Tianming-Liu/CASA0016_ScreenTimer/Src/flip_timer.jpg

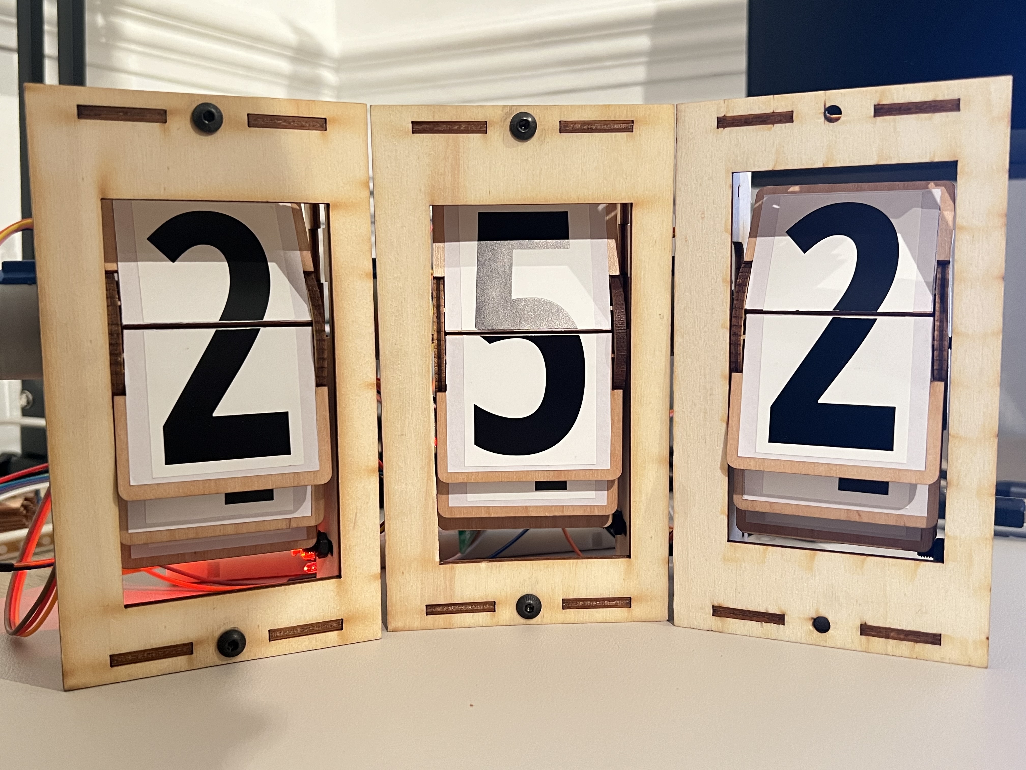
Src/flip_timer.jpg
