Tianming-Liu/CASA0016_ScreenTimer/Src/top00.jpg

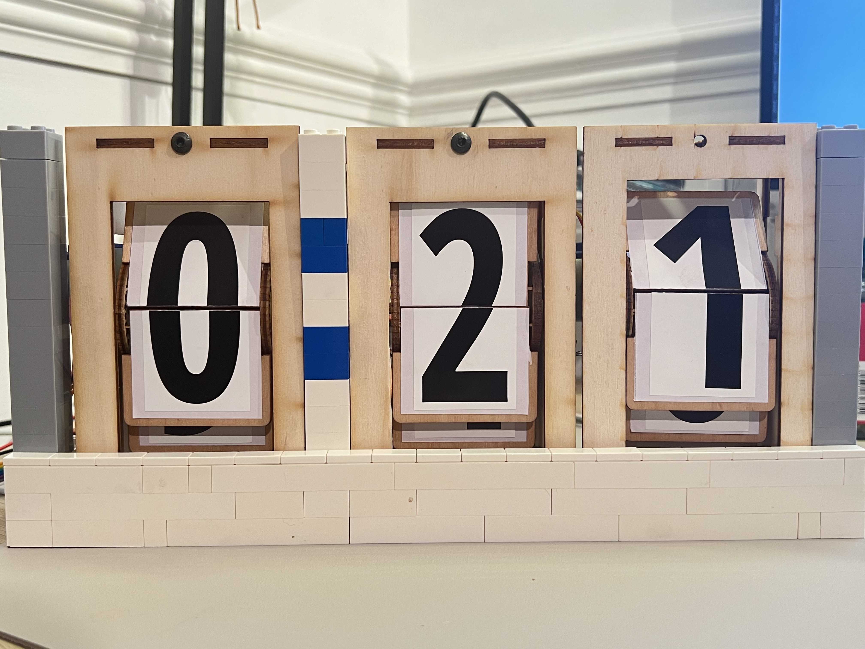
Src/top00.jpg
