Tianming-Liu/CASA0016_ScreenTimer/Src/workspace.jpg

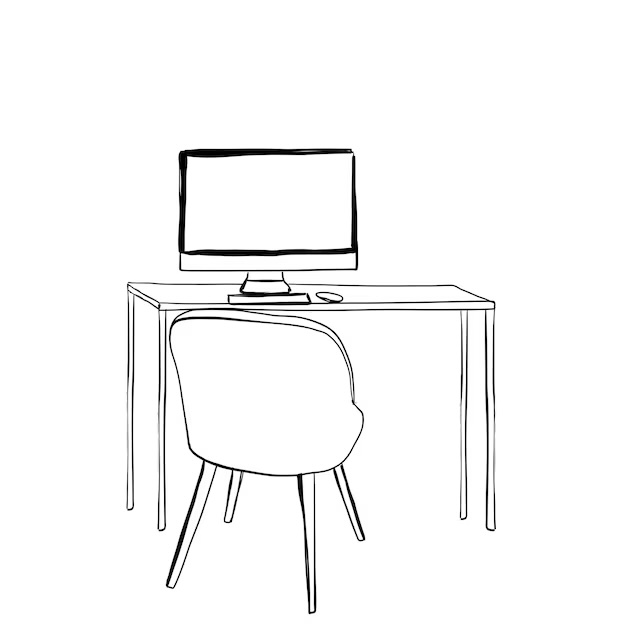
Src/workspace.jpg
